BallBall11/Hitboard/HitboardAir/03_亚克力CAD文件/七星全能版（内测）/七星板布局示意图.png

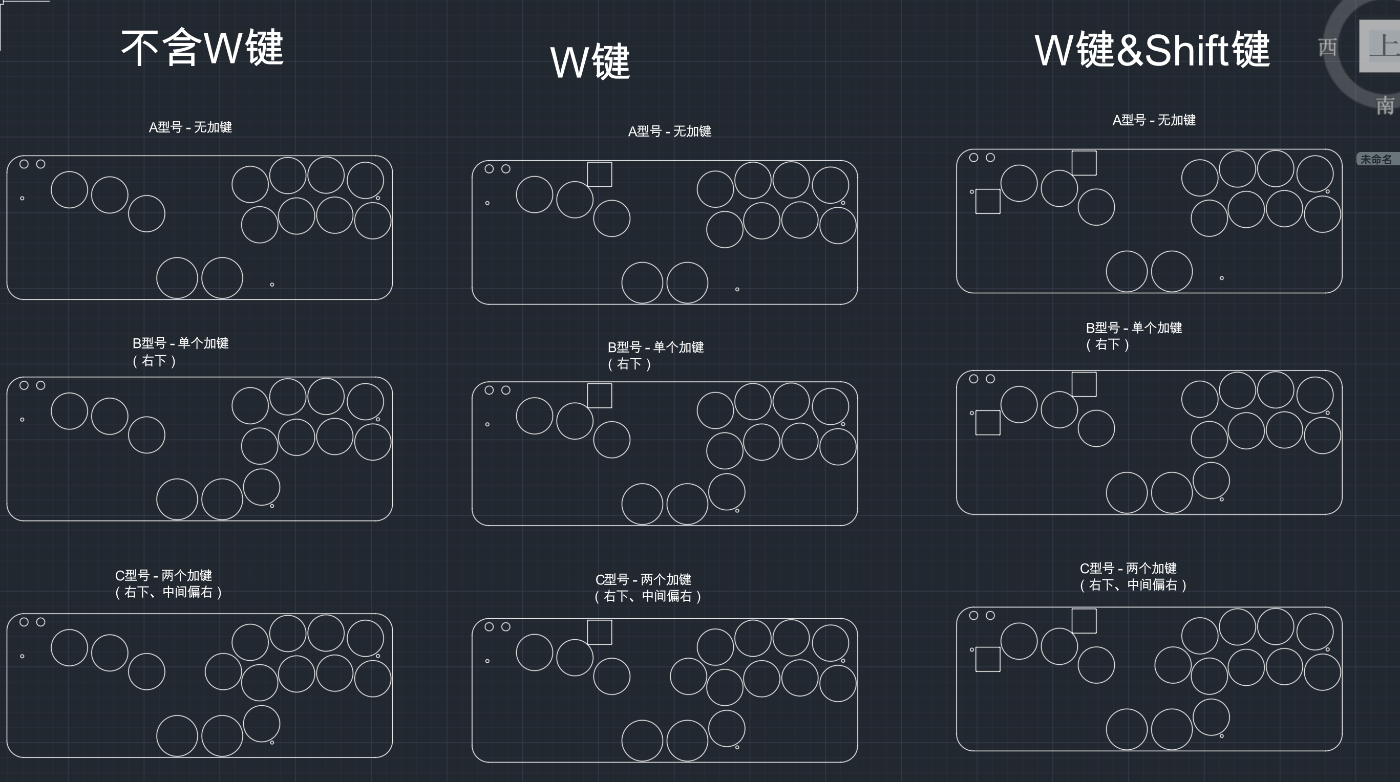
HitboardAir/03_亚克力CAD文件/七星全能版（内测）/七星板布局示意图.png
