BallBall11/Hitboard/HitboardAir/images/FindYourFight03.png

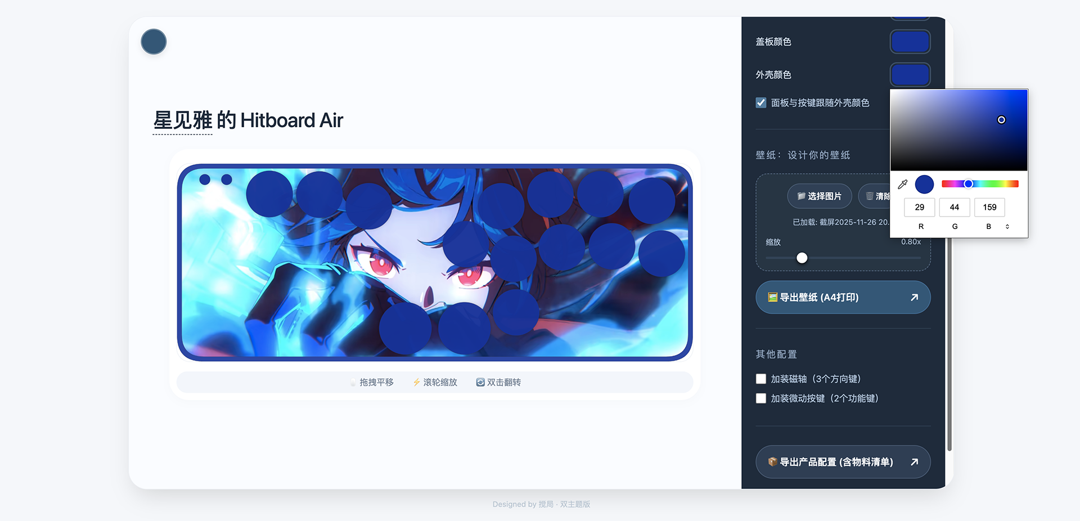
HitboardAir/images/FindYourFight03.png
