BallBall11/Hitboard/HitboardAir/images/FindYourFight04.png

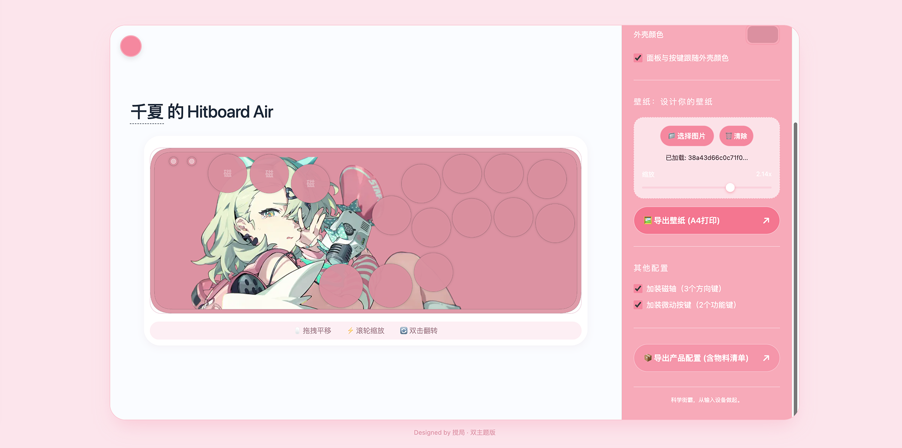
HitboardAir/images/FindYourFight04.png
