BallBall11/Hitboard/HitboardAir/images/边缘对比.JPG

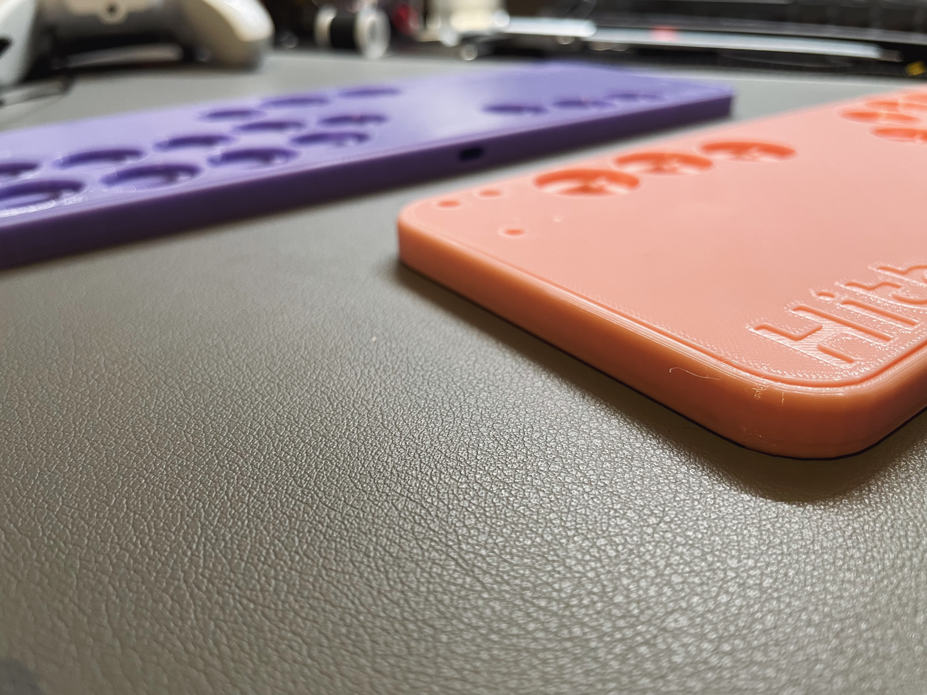
HitboardAir/images/边缘对比.JPG
