BallBall11/Hitboard/HitboardAir/其他/PCB 电路板/功能键电路板/电路板装在03 轴座的左上角.png

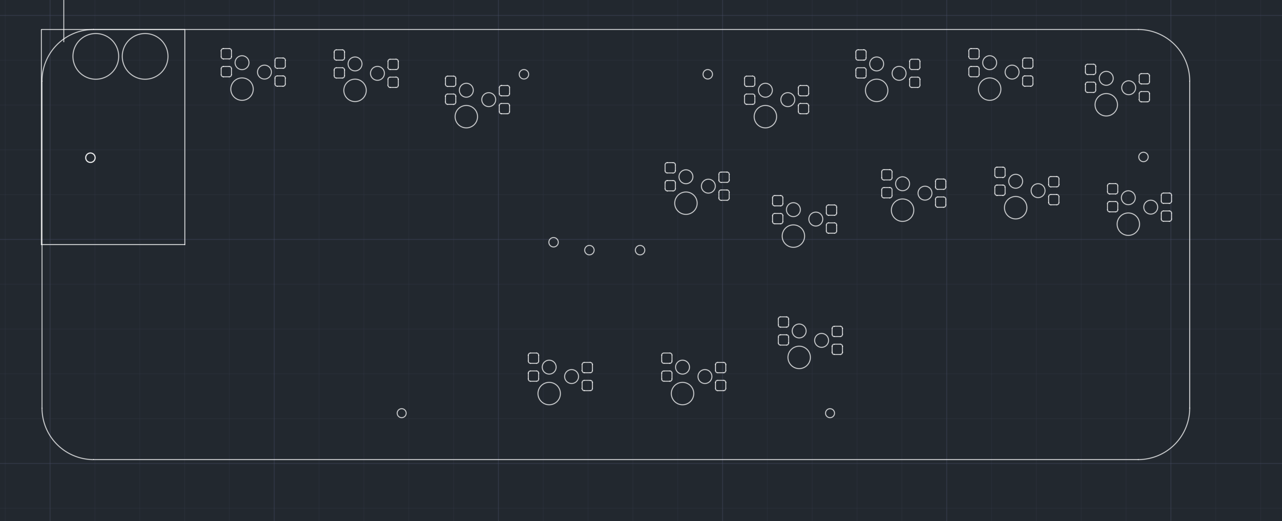
HitboardAir/其他/PCB 电路板/功能键电路板/电路板装在03 轴座的左上角.png
