BallBall11/Hitboard/HitboardZero/03_PCB/功能键电路板/功能键 PCB.png

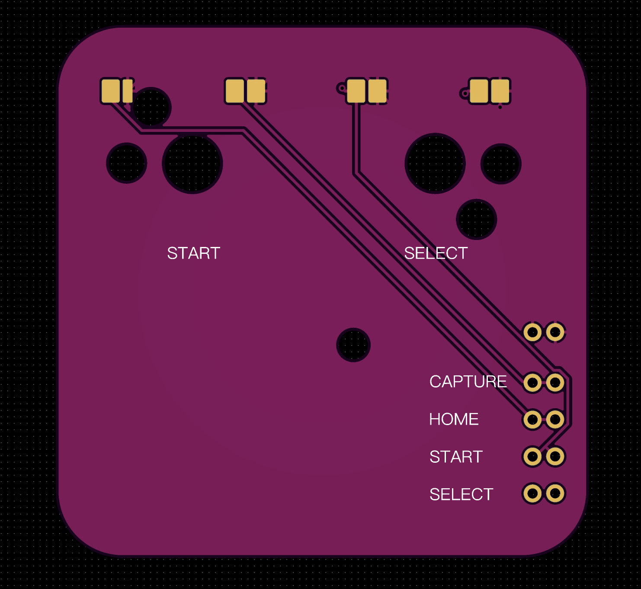
HitboardZero/03_PCB/功能键电路板/功能键 PCB.png
