BallBall11/Hitboard/HitboardAir/02_3D_Files/More - 更多配件 /05_Dock（选配）/05_Dock_下半部分.stl

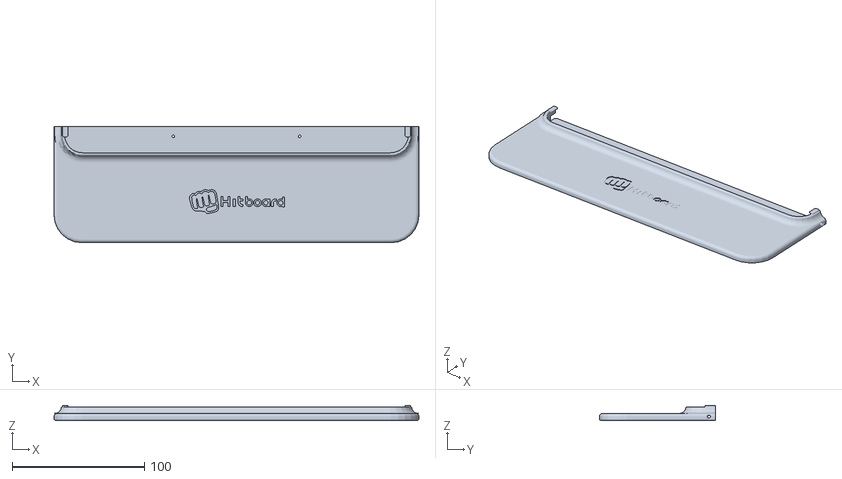
[picture p50: CAD file, 2026-03-08]
HitboardAir/02_3D_Files/More - 更多配件 /05_Dock（选配）/05_Dock_下半部分.stl
276.0 x 88.0 x 11.0
