BallBall11/Hitboard/HitboardAir/02_3D_Files/More - 更多配件 /品牌周边/Hitboard LOGO.stl

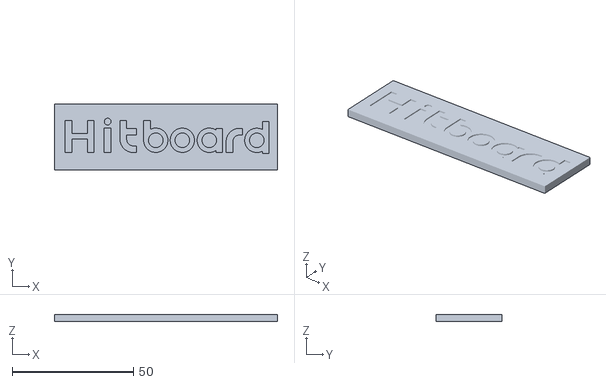
[picture p51: CAD file, 2026-02-25]
HitboardAir/02_3D_Files/More - 更多配件 /品牌周边/Hitboard LOGO.stl
91.9 x 27.1 x 3.00
