BallBall11/Hitboard/HitboardAir/02_3D_Files/Hitboard Air - 七星版（拳皇:绝区零:音游）/More/01 盖板 w.stl

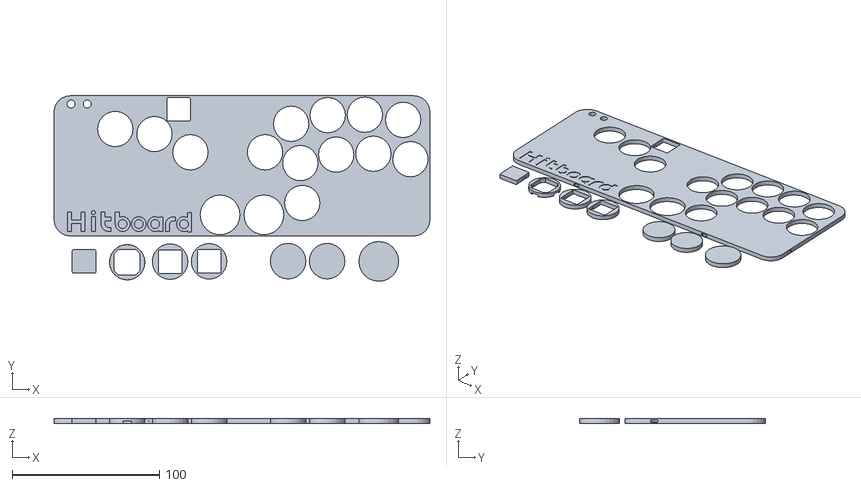
[picture p54: CAD file, 2026-03-18]
HitboardAir/02_3D_Files/Hitboard Air - 七星版（拳皇:绝区零:音游）/More/01 盖板 w.stl
255.2 x 125.9 x 3.40
