BallBall11/Hitboard/HitboardAir/02_3D_Files/More - 更多配件 /00_按键配件/配件_功能键/功能键键帽_妄天使.stl

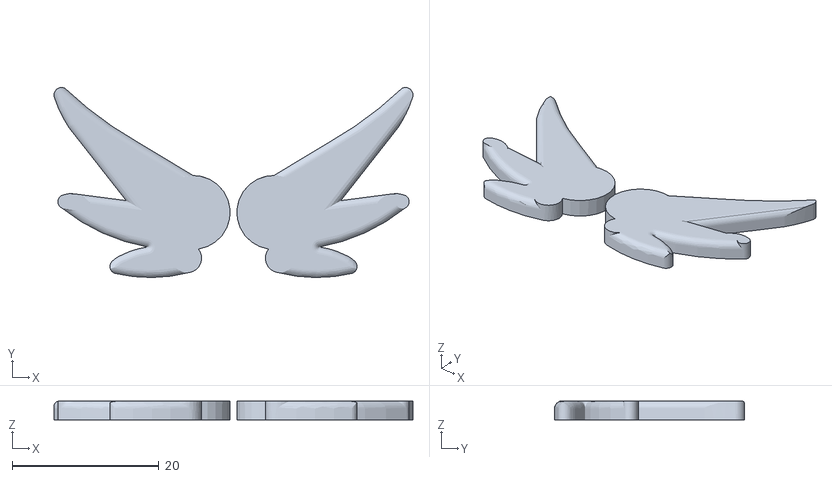
[picture p55: CAD file, 2026-03-14]
HitboardAir/02_3D_Files/More - 更多配件 /00_按键配件/配件_功能键/功能键键帽_妄天使.stl
49.0 x 25.9 x 2.56
