BallBall11/Hitboard/HitboardAir/02_3D_Files/More - 更多配件 /00_按键配件/配件_加键/软糖.stl

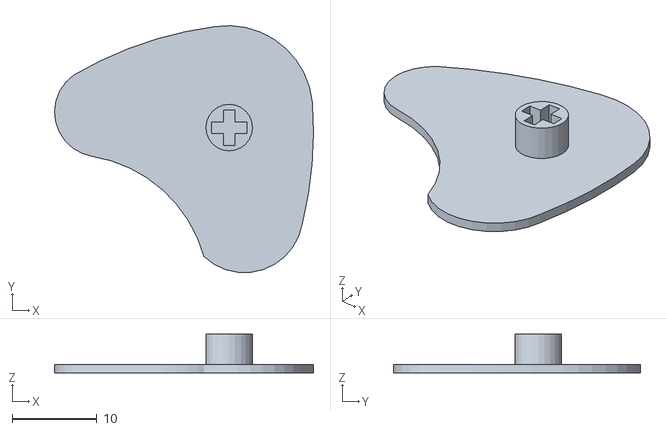
[picture p56: CAD file, 2026-03-11]
HitboardAir/02_3D_Files/More - 更多配件 /00_按键配件/配件_加键/软糖.stl
30.6 x 29.1 x 4.60
