BallBall11/Hitboard/HitboardAir/02_3D_Files/More - 更多配件 /02_盖板配件/w&shfit 封帽.stl

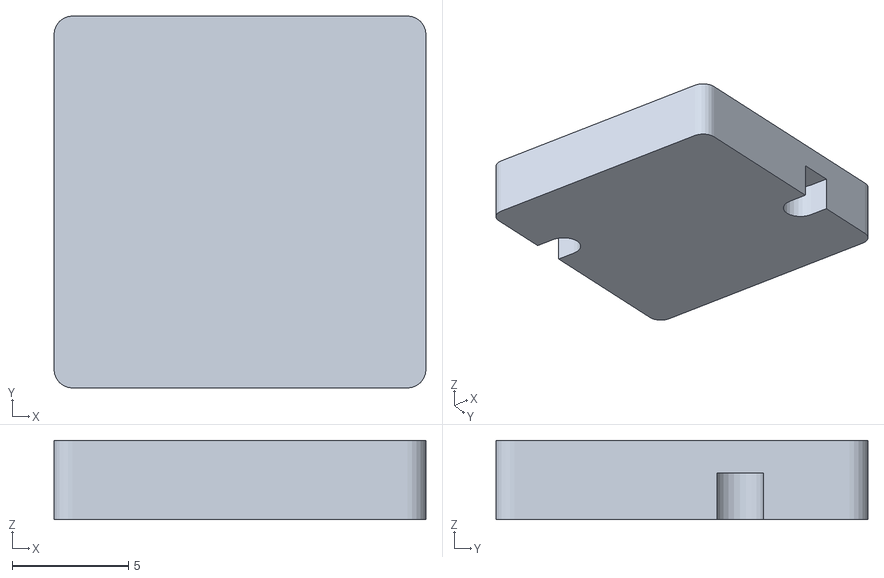
[picture p57: CAD file, 2026-03-16]
HitboardAir/02_3D_Files/More - 更多配件 /02_盖板配件/w&shfit 封帽.stl
16.0 x 16.0 x 3.40
