BallBall11/Hitboard/HitboardAir/02_3D_Files/More - 更多配件 /05_Dock（选配）/05_Dock_上半部分.stl

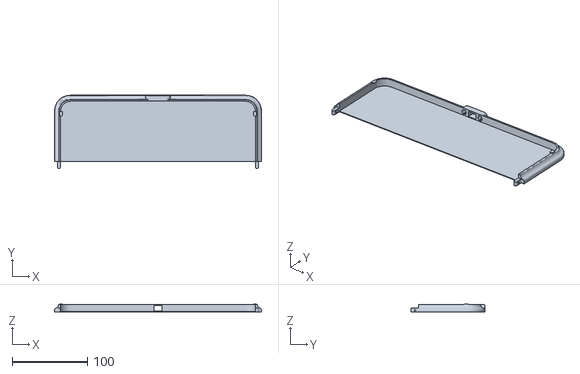
[picture p59: CAD file, 2026-03-07]
HitboardAir/02_3D_Files/More - 更多配件 /05_Dock（选配）/05_Dock_上半部分.stl
276.0 x 98.0 x 11.0
