BallBall11/Hitboard/HitboardAir/02_3D_Files/180x180 打印机（A1mini ）/七星版（可加 w、shift 键）/硬朗/01_盖板_左半.stl

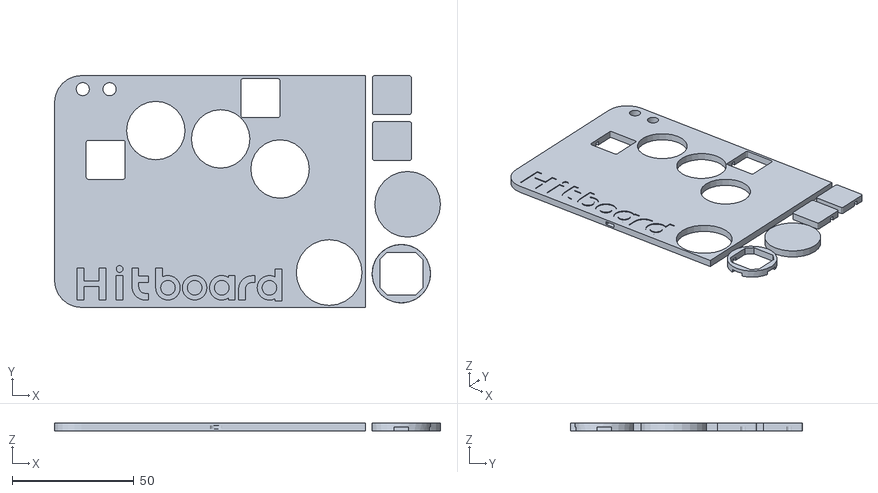
[picture p61: CAD file, 2026-03-19]
HitboardAir/02_3D_Files/180x180 打印机（A1mini ）/七星版（可加 w、shift 键）/硬朗/01_盖板_左半.stl
158.4 x 95.2 x 3.40
