BallBall11/Hitboard/HitboardAir/02_3D_Files/More - 更多配件 /05_Dock（选配）/05_磁吸锁线器.stl

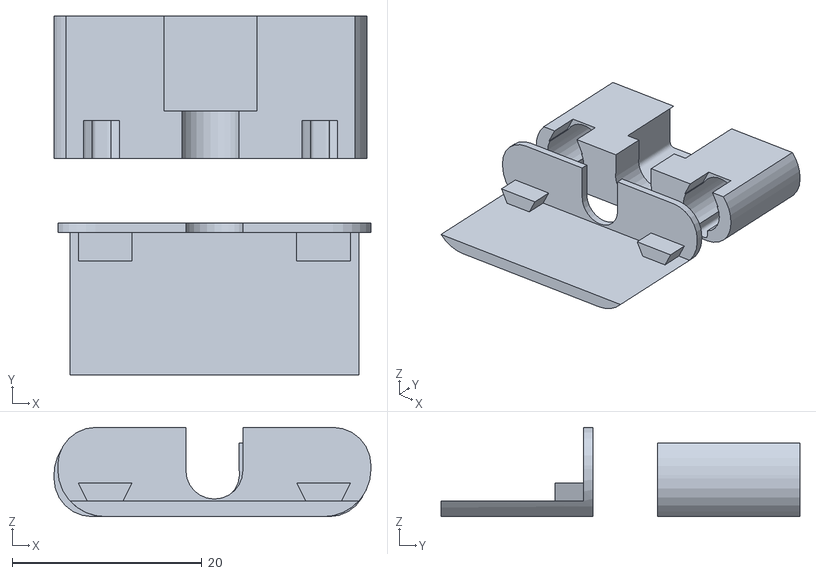
[picture p65: CAD file, 2026-03-06]
HitboardAir/02_3D_Files/More - 更多配件 /05_Dock（选配）/05_磁吸锁线器.stl
33.4 x 37.8 x 9.40
