BallBall11/Hitboard/HitboardAir/02_3D_Files/Hitboard Air - 七星版（拳皇:绝区零:音游）/圆润线条/02 定位板.stl

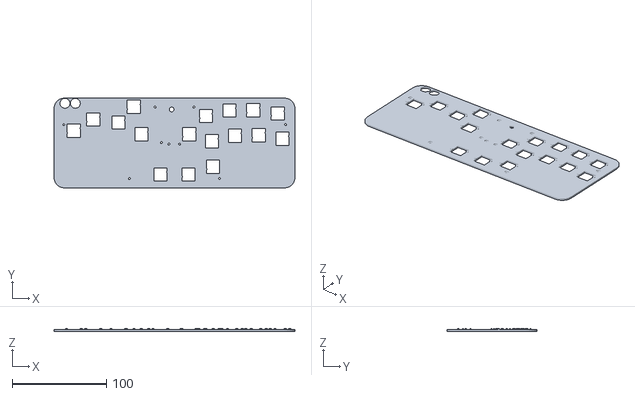
[picture p66: CAD file, 2026-03-16]
HitboardAir/02_3D_Files/Hitboard Air - 七星版（拳皇:绝区零:音游）/圆润线条/02 定位板.stl
255.2 x 95.2 x 3.00
