BallBall11/Hitboard/HitboardAir/02_3D_Files/More - 更多配件 /00_按键配件/配件_功能键/功能键键帽_硬朗.stl

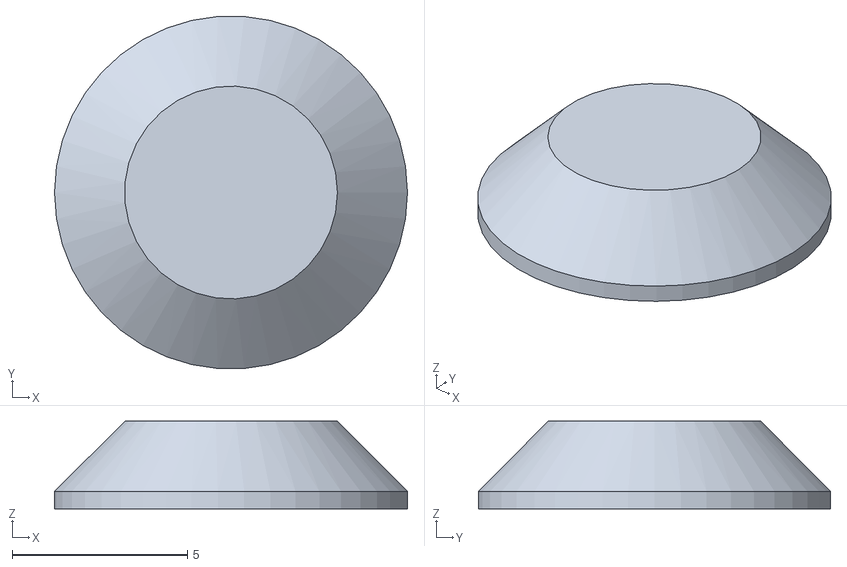
[picture p68: CAD file, 2026-03-14]
HitboardAir/02_3D_Files/More - 更多配件 /00_按键配件/配件_功能键/功能键键帽_硬朗.stl
10.1 x 10.1 x 2.50
