BallBall11/Hitboard/HitboardAir/02_3D_Files/More - 更多配件 /02_盖板配件/26mm 按键封帽_全封.stl

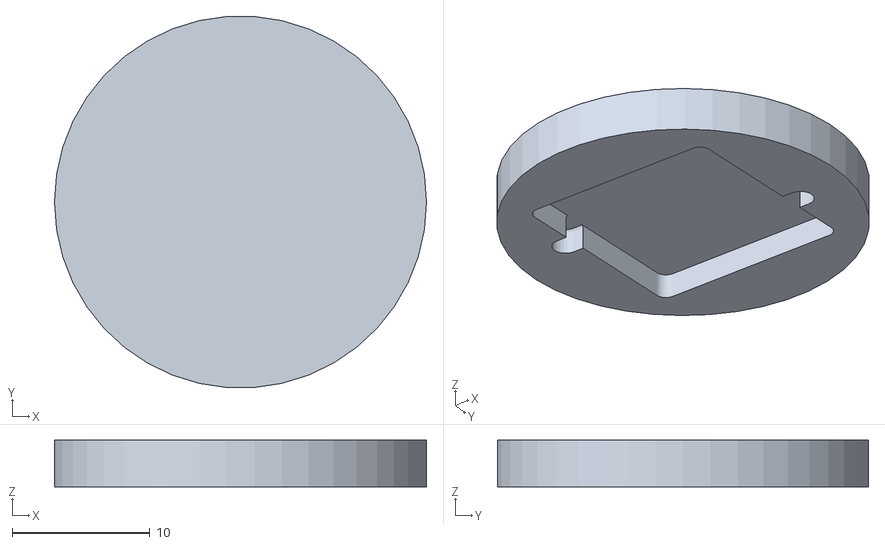
[picture p69: CAD file, 2026-03-14]
HitboardAir/02_3D_Files/More - 更多配件 /02_盖板配件/26mm 按键封帽_全封.stl
27.0 x 26.9 x 3.40
