BallBall11/Hitboard/HitboardAir/02_3D_Files/180x180 打印机（A1mini ）/对称版/圆润/02_定位板_左半.stl

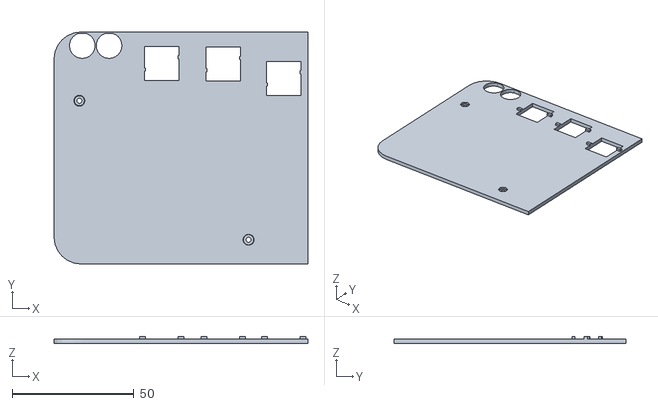
[picture p70: CAD file, 2026-03-18]
HitboardAir/02_3D_Files/180x180 打印机（A1mini ）/对称版/圆润/02_定位板_左半.stl
104.2 x 95.2 x 3.00
