BallBall11/Hitboard/HitboardAir/02_3D_Files/Hitboard Air - 对称版（街霸特调）/圆润线条/02_定位板.stl

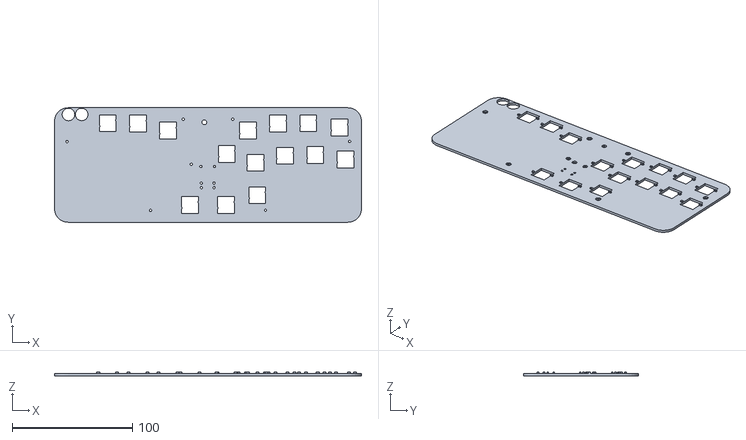
[picture p72: CAD file, 2026-03-12]
HitboardAir/02_3D_Files/Hitboard Air - 对称版（街霸特调）/圆润线条/02_定位板.stl
255.2 x 95.2 x 3.00
