BallBall11/Hitboard/HitboardAir/02_3D_Files/More - 更多配件 /02_盖板配件/23mm 按键封帽_全封.stl

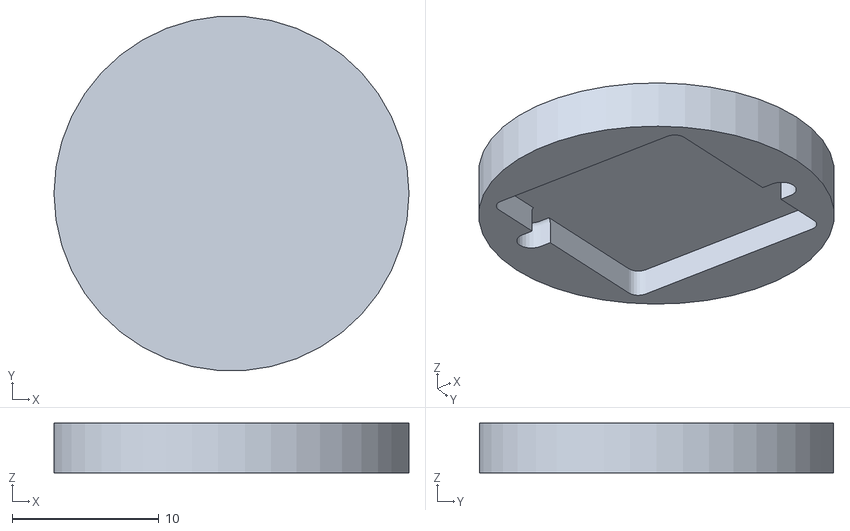
[picture p74: CAD file, 2026-03-13]
HitboardAir/02_3D_Files/More - 更多配件 /02_盖板配件/23mm 按键封帽_全封.stl
24.2 x 24.1 x 3.40
