BallBall11/Hitboard/HitboardAir/02_3D_Files/180x180 打印机（A1mini ）/七星版（可加 w、shift 键）/圆润/02_定位板_右半.stl

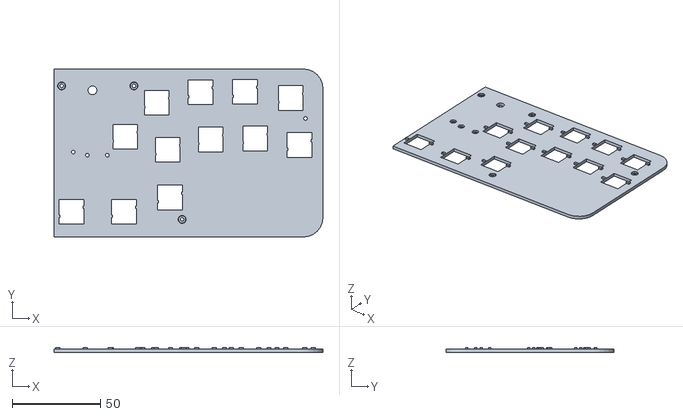
[picture p75: CAD file, 2026-03-19]
HitboardAir/02_3D_Files/180x180 打印机（A1mini ）/七星版（可加 w、shift 键）/圆润/02_定位板_右半.stl
152.4 x 95.2 x 3.00
