BallBall11/Hitboard/HitboardAir/02_3D_Files/180x180 打印机（A1mini ）/对称版/硬朗/03_线路板_右半.stl

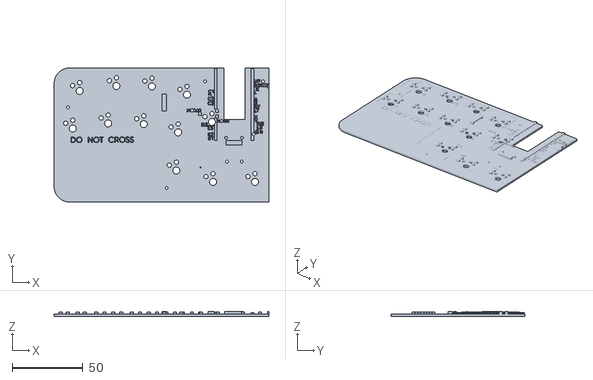
[picture p76: CAD file, 2026-03-18]
HitboardAir/02_3D_Files/180x180 打印机（A1mini ）/对称版/硬朗/03_线路板_右半.stl
152.4 x 95.2 x 3.50
