BallBall11/Hitboard/HitboardAir/02_3D_Files/180x180 打印机（A1mini ）/七星版（可加 w、shift 键）/圆润/02_定位板_左半.stl

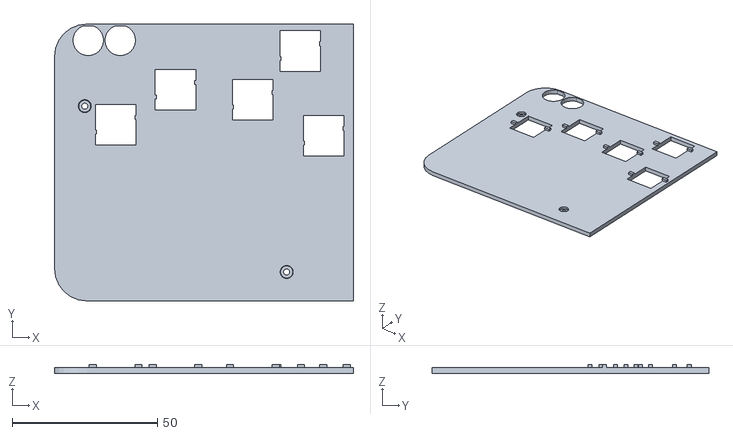
[picture p78: CAD file, 2026-03-18]
HitboardAir/02_3D_Files/180x180 打印机（A1mini ）/七星版（可加 w、shift 键）/圆润/02_定位板_左半.stl
102.8 x 95.2 x 3.00
